matheusgvieira/tcc/firmware/coleta_dados/Core/Src/adc.c

/**
  ******************************************************************************
  * @file    adc.c
  * @brief   This file provides code for the configuration
  *          of the ADC instances.
  ******************************************************************************
  * @attention
  *
  * <h2><center>&copy; Copyright (c) 2021 STMicroelectronics.
  * All rights reserved.</center></h2>
  *
  * This software component is licensed by ST under BSD 3-Clause license,
  * the "License"; You may not use this file except in compliance with the
  * License. You may obtain a copy of the License at:
  *                        opensource.org/licenses/BSD-3-Clause
  *
  ******************************************************************************
  */

/* Includes ------------------------------------------------------------------*/
#include "adc.h"

ADC_HandleTypeDef hadc1;
ADC_HandleTypeDef hadc2;
ADC_HandleTypeDef hadc5;

/* ADC1 init function */
void MX_ADC1_Init(void)
{

  ADC_MultiModeTypeDef multimode = {0};
  ADC_ChannelConfTypeDef sConfig = {0};

  /** Common config
  */
  hadc1.Instance = ADC1;
  hadc1.Init.ClockPrescaler = ADC_CLOCK_SYNC_PCLK_DIV2;
  hadc1.Init.Resolution = ADC_RESOLUTION_12B;
  hadc1.Init.DataAlign = ADC_DATAALIGN_RIGHT;
  hadc1.Init.GainCompensation = 0;
  hadc1.Init.ScanConvMode = ADC_SCAN_DISABLE;
  hadc1.Init.EOCSelection = ADC_EOC_SEQ_CONV;
  hadc1.Init.LowPowerAutoWait = DISABLE;
  hadc1.Init.ContinuousConvMode = DISABLE;
  hadc1.Init.NbrOfConversion = 1;
  hadc1.Init.DiscontinuousConvMode = DISABLE;
  hadc1.Init.ExternalTrigConv = ADC_SOFTWARE_START;
  hadc1.Init.ExternalTrigConvEdge = ADC_EXTERNALTRIGCONVEDGE_NONE;
  hadc1.Init.DMAContinuousRequests = DISABLE;
  hadc1.Init.Overrun = ADC_OVR_DATA_PRESERVED;
  hadc1.Init.OversamplingMode = DISABLE;
  if (HAL_ADC_Init(&hadc1) != HAL_OK)
  {
    Error_Handler();
  }
  /** Configure the ADC multi-mode
  */
  multimode.Mode = ADC_DUALMODE_REGSIMULT;
  multimode.DMAAccessMode = ADC_DMAACCESSMODE_DISABLED;
  multimode.TwoSamplingDelay = ADC_TWOSAMPLINGDELAY_1CYCLE;
  if (HAL_ADCEx_MultiModeConfigChannel(&hadc1, &multimode) != HAL_OK)
  {
    Error_Handler();
  }
  /** Configure Regular Channel
  */
  sConfig.Channel = ADC_CHANNEL_8;
  sConfig.Rank = ADC_REGULAR_RANK_1;
  sConfig.SamplingTime = ADC_SAMPLETIME_2CYCLES_5;
  sConfig.SingleDiff = ADC_SINGLE_ENDED;
  sConfig.OffsetNumber = ADC_OFFSET_NONE;
  sConfig.Offset = 0;
  if (HAL_ADC_ConfigChannel(&hadc1, &sConfig) != HAL_OK)
  {
    Error_Handler();
  }
}
/* ADC2 init function */
void MX_ADC2_Init(void)
{

  ADC_ChannelConfTypeDef sConfig = {0};

  /** Common config
  */
  hadc2.Instance = ADC2;
  hadc2.Init.ClockPrescaler = ADC_CLOCK_SYNC_PCLK_DIV2;
  hadc2.Init.Resolution = ADC_RESOLUTION_12B;
  hadc2.Init.DataAlign = ADC_DATAALIGN_RIGHT;
  hadc2.Init.GainCompensation = 0;
  hadc2.Init.ScanConvMode = ADC_SCAN_DISABLE;
  hadc2.Init.EOCSelection = ADC_EOC_SEQ_CONV;
  hadc2.Init.LowPowerAutoWait = DISABLE;
  hadc2.Init.ContinuousConvMode = DISABLE;
  hadc2.Init.NbrOfConversion = 1;
  hadc2.Init.DiscontinuousConvMode = DISABLE;
  hadc2.Init.DMAContinuousRequests = DISABLE;
  hadc2.Init.Overrun = ADC_OVR_DATA_PRESERVED;
  hadc2.Init.OversamplingMode = DISABLE;
  if (HAL_ADC_Init(&hadc2) != HAL_OK)
  {
    Error_Handler();
  }
  /** Configure Regular Channel
  */
  sConfig.Channel = ADC_CHANNEL_9;
  sConfig.Rank = ADC_REGULAR_RANK_1;
  sConfig.SamplingTime = ADC_SAMPLETIME_2CYCLES_5;
  sConfig.SingleDiff = ADC_SINGLE_ENDED;
  sConfig.OffsetNumber = ADC_OFFSET_NONE;
  sConfig.Offset = 0;
  if (HAL_ADC_ConfigChannel(&hadc2, &sConfig) != HAL_OK)
  {
    Error_Handler();
  }
}
/* ADC5 init function */
void MX_ADC5_Init(void)
{

  ADC_ChannelConfTypeDef sConfig = {0};

  /** Common config
  */
  hadc5.Instance = ADC5;
  hadc5.Init.ClockPrescaler = ADC_CLOCK_SYNC_PCLK_DIV2;
  hadc5.Init.Resolution = ADC_RESOLUTION_12B;
  hadc5.Init.DataAlign = ADC_DATAALIGN_RIGHT;
  hadc5.Init.GainCompensation = 0;
  hadc5.Init.ScanConvMode = ADC_SCAN_DISABLE;
  hadc5.Init.EOCSelection = ADC_EOC_SINGLE_CONV;
  hadc5.Init.LowPowerAutoWait = DISABLE;
  hadc5.Init.ContinuousConvMode = DISABLE;
  hadc5.Init.NbrOfConversion = 1;
  hadc5.Init.DiscontinuousConvMode = DISABLE;
  hadc5.Init.ExternalTrigConv = ADC_SOFTWARE_START;
  hadc5.Init.ExternalTrigConvEdge = ADC_EXTERNALTRIGCONVEDGE_NONE;
  hadc5.Init.DMAContinuousRequests = DISABLE;
  hadc5.Init.Overrun = ADC_OVR_DATA_PRESERVED;
  hadc5.Init.OversamplingMode = DISABLE;
  if (HAL_ADC_Init(&hadc5) != HAL_OK)
  {
    Error_Handler();
  }
  /** Configure Regular Channel
  */
  sConfig.Channel = ADC_CHANNEL_TEMPSENSOR_ADC5;
  sConfig.Rank = ADC_REGULAR_RANK_1;
  sConfig.SamplingTime = ADC_SAMPLETIME_640CYCLES_5;
  sConfig.SingleDiff = ADC_SINGLE_ENDED;
  sConfig.OffsetNumber = ADC_OFFSET_NONE;
  sConfig.Offset = 0;
  if (HAL_ADC_ConfigChannel(&hadc5, &sConfig) != HAL_OK)
  {
    Error_Handler();
  }
}

static uint32_t HAL_RCC_ADC12_CLK_ENABLED=0;

void HAL_ADC_MspInit(ADC_HandleTypeDef* adcHandle)
{

  GPIO_InitTypeDef GPIO_InitStruct = {0};
  if(adcHandle->Instance==ADC1)
  {
    /* ADC1 clock enable */
    HAL_RCC_ADC12_CLK_ENABLED++;
    if(HAL_RCC_ADC12_CLK_ENABLED==1){
      __HAL_RCC_ADC12_CLK_ENABLE();
    }

    __HAL_RCC_GPIOC_CLK_ENABLE();
    /**ADC1 GPIO Configuration
    PC2     ------> ADC1_IN8
    */
    GPIO_InitStruct.Pin = CELL_1_VOLTAGE_Pin;
    GPIO_InitStruct.Mode = GPIO_MODE_ANALOG;
    GPIO_InitStruct.Pull = GPIO_NOPULL;
    HAL_GPIO_Init(CELL_1_VOLTAGE_GPIO_Port, &GPIO_InitStruct);

    /* ADC1 interrupt Init */
    HAL_NVIC_SetPriority(ADC1_2_IRQn, 0, 0);
    HAL_NVIC_EnableIRQ(ADC1_2_IRQn);
  }
  else if(adcHandle->Instance==ADC2)
  {
    /* ADC2 clock enable */
    HAL_RCC_ADC12_CLK_ENABLED++;
    if(HAL_RCC_ADC12_CLK_ENABLED==1){
      __HAL_RCC_ADC12_CLK_ENABLE();
    }

    __HAL_RCC_GPIOC_CLK_ENABLE();
    /**ADC2 GPIO Configuration
    PC3     ------> ADC2_IN9
    */
    GPIO_InitStruct.Pin = CELL_1_CURRENT_Pin;
    GPIO_InitStruct.Mode = GPIO_MODE_ANALOG;
    GPIO_InitStruct.Pull = GPIO_NOPULL;
    HAL_GPIO_Init(CELL_1_CURRENT_GPIO_Port, &GPIO_InitStruct);

    /* ADC2 interrupt Init */
    HAL_NVIC_SetPriority(ADC1_2_IRQn, 0, 0);
    HAL_NVIC_EnableIRQ(ADC1_2_IRQn);
  }
  else if(adcHandle->Instance==ADC5)
  {
    /* ADC5 clock enable */
    __HAL_RCC_ADC345_CLK_ENABLE();

    /* ADC5 interrupt Init */
    HAL_NVIC_SetPriority(ADC5_IRQn, 0, 0);
    HAL_NVIC_EnableIRQ(ADC5_IRQn);
  }
}

void HAL_ADC_MspDeInit(ADC_HandleTypeDef* adcHandle)
{

  if(adcHandle->Instance==ADC1)
  {
    /* Peripheral clock disable */
    HAL_RCC_ADC12_CLK_ENABLED--;
    if(HAL_RCC_ADC12_CLK_ENABLED==0){
      __HAL_RCC_ADC12_CLK_DISABLE();
    }

    /**ADC1 GPIO Configuration
    PC2     ------> ADC1_IN8
    */
    HAL_GPIO_DeInit(CELL_1_VOLTAGE_GPIO_Port, CELL_1_VOLTAGE_Pin);

    /* ADC1 interrupt Deinit */
  /* USER CODE BEGIN ADC1:ADC1_2_IRQn disable */
    /**
    * Uncomment the line below to disable the "ADC1_2_IRQn" interrupt
    * Be aware, disabling shared interrupt may affect other IPs
    */
    /* HAL_NVIC_DisableIRQ(ADC1_2_IRQn); */
  /* USER CODE END ADC1:ADC1_2_IRQn disable */

  }
  else if(adcHandle->Instance==ADC2)
  {
    /* Peripheral clock disable */
    HAL_RCC_ADC12_CLK_ENABLED--;
    if(HAL_RCC_ADC12_CLK_ENABLED==0){
      __HAL_RCC_ADC12_CLK_DISABLE();
    }

    /**ADC2 GPIO Configuration
    PC3     ------> ADC2_IN9
    */
    HAL_GPIO_DeInit(CELL_1_CURRENT_GPIO_Port, CELL_1_CURRENT_Pin);

    /* ADC2 interrupt Deinit */
  /* USER CODE BEGIN ADC2:ADC1_2_IRQn disable */
    /**
    * Uncomment the line below to disable the "ADC1_2_IRQn" interrupt
    * Be aware, disabling shared interrupt may affect other IPs
    */
    /* HAL_NVIC_DisableIRQ(ADC1_2_IRQn); */
  /* USER CODE END ADC2:ADC1_2_IRQn disable */

  }
  else if(adcHandle->Instance==ADC5)
  {
    /* Peripheral clock disable */
    __HAL_RCC_ADC345_CLK_DISABLE();

    /* ADC5 interrupt Deinit */
    HAL_NVIC_DisableIRQ(ADC5_IRQn);
  }
}

/************************ (C) COPYRIGHT STMicroelectronics *****END OF FILE****/
