matheusgvieira/tcc/firmware/comunicacao/components/events.c

#include "events.h"

extern TaskHandle_t mqtt_task_handle;

void mqtt_event_handler_publish(void *handler_args, esp_event_base_t base, int32_t event_id, void *event_data)
{
    esp_mqtt_event_handle_t event = event_data;
    switch ((esp_mqtt_event_id_t)event_id) {
        case MQTT_EVENT_CONNECTED:
            printf("MQTT_EVENT_CONNECTED\n");
            xTaskNotify(mqtt_task_handle, MQTT_CONNECTED, eSetValueWithOverwrite);
            break;
        case MQTT_EVENT_DISCONNECTED:
            printf("MQTT_EVENT_DISCONNECTED\n");
            xTaskNotify(mqtt_task_handle, MQTT_DISCONNECTED, eSetValueWithOverwrite);
            break;
        case MQTT_EVENT_SUBSCRIBED:
            printf("MQTT_EVENT_SUBSCRIBED, msg_id=%d\n", event->msg_id);
            break;
        case MQTT_EVENT_UNSUBSCRIBED:
            printf("MQTT_EVENT_UNSUBSCRIBED, msg_id=%d\n", event->msg_id);
            break;
        case MQTT_EVENT_PUBLISHED:
            printf("MQTT_EVENT_PUBLISHED, msg_id=%d\n", event->msg_id);
            break;
        case MQTT_EVENT_DATA:
            printf("MQTT_EVENT_DATA\n");
            break;
        case MQTT_EVENT_ERROR:
            printf("MQTT_EVENT_ERROR\n");
            break;
        default:
            printf("Other event id:%d\n", event->event_id);
            break;
    }
}
