matheusgvieira/tcc/firmware/comunicacao/components/include/wifi.h

#pragma once

#include <esp_wifi.h>
#include <esp_event.h>
#include <esp_log.h>
#include <esp_system.h>
#include <nvs_flash.h>
#include <sys/param.h>
#include "nvs_flash.h"
#include "esp_netif.h"
#include "esp_eth.h"
#include "esp_tls_crypto.h"
#include <esp_http_server.h>
#include <string.h>
#include "freertos/FreeRTOS.h"
#include "freertos/task.h"
#include "freertos/event_groups.h"
#include "esp_mac.h"
#include "cJSON.h"
#include "lwip/err.h"
#include "lwip/sys.h"
#include "generic_digital_output.h"

#ifdef __cplusplus
extern "C" {
#endif

// Defines
#define EXAMPLE_ESP_WIFI_CHANNEL   1
#define EXAMPLE_MAX_STA_CONN       4
#define EXAMPLE_ESP_MAXIMUM_RETRY  5
#define WIFI_CONNECTED_BIT BIT0
#define WIFI_FAIL_BIT      BIT1

// Struct
typedef struct {
    char * ssid;
    char * password;
} wifi_credentials;

// Functions
void get_wifi_credentials(wifi_credentials *credentials);
bool check_credentials(wifi_credentials *credentials);
int reset_wifi_credentials();

int8_t wifi_connect_sta(wifi_credentials *credentials);
void setup_wifi();


#ifdef __cplusplus
}
#endif
